tshea113/MSCan_Gauge-1/SquirtView/GaugeData.h

// Constants
const int kNumViews                     = 4;      // Number of gauge views
const int kNumSettings                  = 5;      // Number of settings
const int kNumGauges                    = 16;     // Number of gauges
const int kNumGraphs                    = 3;      // Number of graph gauges

const String kViews[kNumViews] = {"Dashboard", "Single", "Graph", "Settings"};
const String kSettings[kNumSettings] = {"LED Ring", "Shift RPM", "Warnings", "Coolant Warn", "Exit"};
const String kGauges[kNumGauges] = {"RPM", "AFR", "Coolant", "MAP", "MAT", "Timing", "Voltage", "TPS", "Knock", "Barometer", "EGO Corr", "IAC", "Spark Dwell", "Boost Duty", "Idle Target", "AFR Target"};
const String kGraphs[kNumGraphs] = {"AFR", "MAP", "MAT"};

enum ViewsMenu : uint8_t
{
  kDashboardView = 0,
  kSingleView = 1,
  kGraphView = 2,
  kSettingView = 3
};

enum SettingMenu : uint8_t
{
  kLedRingEnableSetting = 0,
  kShiftRPMSetting = 1,
  kWarningsEnableSetting = 2,
  kCoolantWarningSetting = 3,
  kExitSetting = 4
};

enum Gauges : uint8_t
{
  kRPMGauge = 0,
  kAFRGauge = 1,
  kCoolantGauge = 2,
  kMAPGauge = 3,
  kMATGauge = 4,
  kTimingGauge = 5,
  kVoltageGauge = 6,
  kTPSGauge = 7,
  kKnockGauge = 8,
  kBarometerGauge = 9,
  kEGOCorrectionGauge = 10,
  kIACGauge = 11,
  kSparkDwellGauge = 12,
  kBoostDutyGauge = 13,
  kIdleTargetGauge = 14,
  kAfrTargetGauge = 15
};

enum Graphs : uint8_t
{
  kAFRGraph = 0,
  kMAPGraph = 1,
  kMATGraph = 2
};

// EEPROM Addresses
const uint8_t kEEPROMInitAddr     = 0;
const uint8_t kRingEnableAddr     = 1;
const uint8_t kShiftRpmAddr       = 2;
const uint8_t kWarningEnableAddr  = 4;
const uint8_t kCoolantWarningAddr = 5;

const uint8_t kEEPROMValidId = 4;

// Data Structures
struct MenuState
{
  bool inMenu = false;
  bool inSettings = false;
  bool settingSelect = false;
  uint8_t menuPos = 0;
  uint8_t settingsPos = 0;
  uint8_t gaugeSinglePos = 0;
  uint8_t gaugeGraphPos = 0;
};

struct Settings
{
  bool dirty = false;
  bool LEDRingEnable = true;
  uint16_t shiftRPM = 6800;
  bool warningsEnable = true;
  uint16_t coolantWarning = 240;
};

struct GaugeData
{
  unsigned int RPM;
  unsigned int CLT;
  unsigned int MAP;
  unsigned int MAT;
  unsigned int SPKADV;
  unsigned int BATTV;
  unsigned int TPS;
  unsigned int Knock;
  unsigned int Baro;
  unsigned int EGOc;
  unsigned int IAC;
  unsigned int dwell;
  unsigned int bstduty;
  unsigned int idle_tar;
  int AFR;
  int AFR_tar;
  unsigned int MAP_highest;
  unsigned int RPM_highest;
  unsigned int CLT_highest;
  unsigned int MAT_highest;
  unsigned int Knock_highest;
  int AFR_highest;
  int AFR_lowest;
  uint8_t engine;
  uint8_t CEL;
  uint8_t status1;
  uint8_t status2;
  uint8_t status3;
  uint8_t status6;
  uint8_t status7;
};
